ifilot/p2000t-teletekst-cartridge/emulator/src/p2wp_device.c

#include "p2wp_device.h"
#include "../../firmware/src/firmware_core.h"
#include "../../firmware/src/custom_endpoint.h"
#include "../../firmware/src/version.h"

#include <stdbool.h>
#include <stdio.h>
#include <string.h>

enum {
    TX_PORT = 0x40,
    RX_PORT = 0x41,
    STATUS_PORT = 0x42,
    SCREEN_SIZE = 960,
    CHUNK_SIZE = 240,
    FETCH_TIMEOUT_TICKS = 3000,
};

static p2wp_parser_t parser;
static p2wp_firmware_core_t firmware_core;
static p2wp_fetch_fn fetch_page;
static void *fetch_context;
static uint8_t encoded[P2WP_MAX_ENCODED];
static size_t encoded_length;
static size_t encoded_position;
static uint8_t screen[SCREEN_SIZE];
static uint8_t next_subpage;
static uint8_t local_clock[7];
static uint16_t previous_page, next_page;
static uint8_t fetch_state;
static uint8_t fetch_error;
static uint8_t profile_state;
static uint8_t wifi_security;
static uint8_t protocol_maximum = P2WP_MAX_VERSION;
static uint8_t status_length_override;
static int fetch_stall_after = -1;
static unsigned fetch_start_count;
static unsigned fetch_stall_ticks;
static bool fetch_timeout_enabled = true;
static bool clock_valid = true;
static const char *flash_path;
static char stored_custom_url[CUSTOM_ENDPOINT_URL_MAX + 1u];
static uint8_t stored_custom_url_length;
static uint8_t stored_auto_start_source = P2WP_TELETEKST_AUTOSTART_DISABLED;

static const uint8_t flash_magic[8] = {
    'P', '2', 'W', 'P', 'U', 'R', 'L', '1',
};

static uint8_t emulator_capabilities(void *context) {
    (void)context;
    return protocol_maximum >= 3u
        ? P2WP_CAPABILITY_ECHO | P2WP_CAPABILITY_WIFI |
            P2WP_CAPABILITY_INTERNET | P2WP_CAPABILITY_WIFI_PROFILE |
            P2WP_CAPABILITY_DEVICE_INFO | P2WP_CAPABILITY_VERSION_CHECK
        : P2WP_CAPABILITY_ECHO | P2WP_CAPABILITY_WIFI |
            P2WP_CAPABILITY_INTERNET | P2WP_CAPABILITY_WIFI_PROFILE;
}

static uint8_t version_check_start(
    void *context,
    const p2wp_frame_t *request,
    p2wp_frame_t *response
) {
    (void)context;
    (void)request;
    response->payload_length = 0u;
    return P2WP_FIRMWARE_COMMAND_OK;
}

static uint8_t version_check_status(
    void *context,
    const p2wp_frame_t *request,
    p2wp_frame_t *response
) {
    (void)context;
    (void)request;
    response->payload[0] = P2WP_VERSION_CHECK_COMPLETE;
    response->payload[1] = 0u;
    response->payload[2] = P2WP_FIRMWARE_VERSION_MAJOR;
    response->payload[3] = P2WP_FIRMWARE_VERSION_MINOR;
    response->payload[4] = P2WP_FIRMWARE_VERSION_PATCH;
    response->payload_length = 5u;
    return P2WP_FIRMWARE_COMMAND_OK;
}

static uint8_t wifi_scan_start(
    void *context,
    const p2wp_frame_t *request,
    p2wp_frame_t *response
) {
    (void)context;
    (void)request;
    response->payload_length = 0u;
    return P2WP_FIRMWARE_COMMAND_OK;
}

static uint8_t wifi_scan_status(
    void *context,
    const p2wp_frame_t *request,
    p2wp_frame_t *response
) {
    (void)context;
    (void)request;
    response->payload[0] = 2u;
    response->payload[1] = 1u;
    response->payload[2] = 1u;
    response->payload_length = 3u;
    return P2WP_FIRMWARE_COMMAND_OK;
}

static uint8_t wifi_scan_result(
    void *context,
    const p2wp_frame_t *request,
    p2wp_frame_t *response
) {
    (void)context;
    static const char ssid[] = "Emulated WiFi";
    response->payload[0] = request->payload[0];
    response->payload[1] = (uint8_t)-35;
    response->payload[2] = wifi_security;
    response->payload[3] = sizeof(ssid) - 1u;
    memcpy(response->payload + 4u, ssid, sizeof(ssid) - 1u);
    response->payload_length = 4u + sizeof(ssid) - 1u;
    return P2WP_FIRMWARE_COMMAND_OK;
}

static uint8_t wifi_connect(
    void *context,
    const p2wp_frame_t *request,
    p2wp_frame_t *response
) {
    (void)context;
    if ((wifi_security == 0u && request->payload[1] != 0u) ||
        (wifi_security == 1u && request->payload[1] < 8u)) {
        return P2WP_ERROR_INVALID_PAYLOAD;
    }
    response->payload_length = 0u;
    return P2WP_FIRMWARE_COMMAND_OK;
}

static uint8_t wifi_status(
    void *context,
    const p2wp_frame_t *request,
    p2wp_frame_t *response
) {
    (void)context;
    (void)request;
    response->payload[0] = 2u;
    response->payload_length = 1u;
    return P2WP_FIRMWARE_COMMAND_OK;
}

static uint8_t wifi_profile_status(
    void *context,
    const p2wp_frame_t *request,
    p2wp_frame_t *response
) {
    (void)context;
    (void)request;
    response->payload[0] = profile_state;
    response->payload[1] = 0u;
    response->payload_length = 2u;
    return P2WP_FIRMWARE_COMMAND_OK;
}

static uint8_t wifi_profile_connect(
    void *context,
    const p2wp_frame_t *request,
    p2wp_frame_t *response
) {
    (void)context;
    (void)request;
    response->payload_length = 0u;
    return profile_state != 0u
        ? P2WP_FIRMWARE_COMMAND_OK
        : P2WP_ERROR_WIFI_BUSY;
}

static uint8_t wifi_profile_save(
    void *context,
    const p2wp_frame_t *request,
    p2wp_frame_t *response
) {
    (void)context;
    (void)request;
    profile_state = 1u;
    response->payload_length = 0u;
    return P2WP_FIRMWARE_COMMAND_OK;
}

static uint8_t wifi_profile_delete(
    void *context,
    const p2wp_frame_t *request,
    p2wp_frame_t *response
) {
    (void)context;
    (void)request;
    profile_state = 0u;
    response->payload_length = 0u;
    return P2WP_FIRMWARE_COMMAND_OK;
}

static uint8_t teletekst_fetch_start(
    void *context,
    const p2wp_frame_t *request,
    p2wp_frame_t *response
) {
    (void)context;
    const uint16_t page =
        (uint16_t)request->payload[0] |
        ((uint16_t)request->payload[1] << 8u);
    char custom_url[97] = {0};
    if (request->payload[3] == P2WP_TELETEKST_SOURCE_CUSTOM) {
        memcpy(custom_url, request->payload + 5u, request->payload[4]);
    }
    if (request->payload[3] == P2WP_TELETEKST_SOURCE_INTERNATIONAL) {
        if (request->payload[4] == PETSCII_CATALOGUE) {
            fetch_error = petscii_catalogue(request->payload[2], screen)
                ? 0u : P2WP_TELETEKST_ERROR_INVALID_DATA;
            next_subpage = 0u;
            previous_page = next_page = 0u;
            fetch_state = fetch_error ? 4u : 3u;
            response->payload_length = 0u;
            return P2WP_FIRMWARE_COMMAND_OK;
        }
        if (!petscii_channel_url(request->payload[4], custom_url, sizeof(custom_url)))
            return P2WP_ERROR_INVALID_PAYLOAD;
    }
    previous_page = 0u;
    next_page = 0u;
    if (fetch_stall_after >= 0 &&
        fetch_start_count >= (unsigned)fetch_stall_after) {
        fetch_error = 0u;
        fetch_state = 1u;
        fetch_stall_ticks = 0u;
        response->payload_length = 0u;
        return P2WP_FIRMWARE_COMMAND_OK;
    }
    fetch_start_count++;
    fetch_error = fetch_page != NULL ? fetch_page(
        fetch_context,
        request->payload[3],
        custom_url[0] != '\0' ? custom_url : NULL,
        page,
        request->payload[2],
        screen,
        &next_subpage,
        &previous_page,
        &next_page,
        local_clock
    ) : P2WP_TELETEKST_ERROR_INVALID_DATA;
    fetch_state = fetch_error != 0u ? 4u : 3u;
    response->payload_length = 0u;
    return P2WP_FIRMWARE_COMMAND_OK;
}

static uint8_t teletekst_fetch_status(
    void *context,
    const p2wp_frame_t *request,
    p2wp_frame_t *response
) {
    (void)context;
    response->payload[0] = fetch_state;
    response->payload[1] = request->version < 7u &&
        fetch_error >= P2WP_TELETEKST_ERROR_DNS
            ? P2WP_TELETEKST_ERROR_NETWORK
            : fetch_error;
    response->payload[4] = next_subpage;
    if (request->version >= 3u || status_length_override >= 9u) {
        memcpy(response->payload + 5u, local_clock, 3u);
        response->payload[8] = fetch_error != 0u || !clock_valid ? 0u : 1u;
        memcpy(response->payload + 9u, local_clock + 3u, 4u);
        if (request->version >= 4u) {
            response->payload[13] = (uint8_t)previous_page;
            response->payload[14] = (uint8_t)(previous_page >> 8u);
            response->payload[15] = (uint8_t)next_page;
            response->payload[16] = (uint8_t)(next_page >> 8u);
            if (request->version >= 7u) {
                response->payload[17] = 0u;
                response->payload[18] = 0u;
                response->payload[19] = 0u;
                response->payload[20] = 0u;
            }
        }
        response->payload_length = status_length_override != 0u
            ? status_length_override
            : (request->version >= 7u
                ? 21u
                : (request->version >= 4u ? 17u : 13u));
    } else {
        response->payload_length = status_length_override != 0u
            ? status_length_override
            : 5u;
    }
    return P2WP_FIRMWARE_COMMAND_OK;
}

static uint8_t teletekst_fetch_rows(
    void *context,
    const p2wp_frame_t *request,
    p2wp_frame_t *response
) {
    (void)context;
    memcpy(
        response->payload,
        screen + (size_t)request->payload[0] * CHUNK_SIZE,
        CHUNK_SIZE
    );
    response->payload_length = CHUNK_SIZE;
    return P2WP_FIRMWARE_COMMAND_OK;
}

static uint8_t teletekst_custom_url_load(
    void *context,
    const p2wp_frame_t *request,
    p2wp_frame_t *response
) {
    (void)context;
    (void)request;
    response->payload[0] = stored_custom_url_length;
    memcpy(
        response->payload + 1u,
        stored_custom_url,
        stored_custom_url_length
    );
    response->payload_length = (uint16_t)(1u + stored_custom_url_length);
    return P2WP_FIRMWARE_COMMAND_OK;
}

static bool write_flash_settings(void) {
    if (flash_path == NULL) {
        return true;
    }
    FILE *file = fopen(flash_path, "wb");
    if (file == NULL) {
        return false;
    }
    const uint8_t format_marker = 0xfeu;
    const bool wrote = fwrite(flash_magic, 1u, sizeof(flash_magic), file) ==
            sizeof(flash_magic) &&
        fwrite(&format_marker, 1u, 1u, file) == 1u &&
        fwrite(&stored_auto_start_source, 1u, 1u, file) == 1u &&
        fwrite(&stored_custom_url_length, 1u, 1u, file) == 1u &&
        fwrite(stored_custom_url, 1u, stored_custom_url_length, file) ==
            stored_custom_url_length;
    return fclose(file) == 0 && wrote;
}

static uint8_t teletekst_custom_url_save(
    void *context,
    const p2wp_frame_t *request,
    p2wp_frame_t *response
) {
    (void)context;
    const uint8_t url_length = request->payload[0];
    custom_endpoint_t endpoint;
    if (!custom_endpoint_parse(
            (const char *)request->payload + 1u,
            url_length,
            &endpoint
        )) {
        return P2WP_ERROR_INVALID_PAYLOAD;
    }
    if (stored_custom_url_length == url_length &&
        memcmp(stored_custom_url, request->payload + 1u, url_length) == 0) {
        response->payload_length = 0u;
        return P2WP_FIRMWARE_COMMAND_OK;
    }
    char previous_url[CUSTOM_ENDPOINT_URL_MAX + 1u];
    const uint8_t previous_length = stored_custom_url_length;
    memcpy(previous_url, stored_custom_url, sizeof(previous_url));
    memcpy(stored_custom_url, request->payload + 1u, url_length);
    stored_custom_url[url_length] = '\0';
    stored_custom_url_length = url_length;
    if (!write_flash_settings()) {
        memcpy(stored_custom_url, previous_url, sizeof(previous_url));
        stored_custom_url_length = previous_length;
        return P2WP_ERROR_INTERNAL;
    }
    response->payload_length = 0u;
    return P2WP_FIRMWARE_COMMAND_OK;
}

static uint8_t teletekst_settings_load(
    void *context,
    const p2wp_frame_t *request,
    p2wp_frame_t *response
) {
    (void)context;
    (void)request;
    response->payload[0] = stored_auto_start_source;
    response->payload_length = 1u;
    return P2WP_FIRMWARE_COMMAND_OK;
}

static uint8_t teletekst_settings_save(
    void *context,
    const p2wp_frame_t *request,
    p2wp_frame_t *response
) {
    (void)context;
    const uint8_t previous = stored_auto_start_source;
    stored_auto_start_source = request->payload[0];
    if (!write_flash_settings()) {
        stored_auto_start_source = previous;
        return P2WP_ERROR_INTERNAL;
    }
    response->payload_length = 0u;
    return P2WP_FIRMWARE_COMMAND_OK;
}

static const p2wp_firmware_operations_t emulator_operations = {
    .capabilities = emulator_capabilities,
    .version_check_start = version_check_start,
    .version_check_status = version_check_status,
    .wifi_scan_start = wifi_scan_start,
    .wifi_scan_status = wifi_scan_status,
    .wifi_scan_result = wifi_scan_result,
    .wifi_connect = wifi_connect,
    .wifi_status = wifi_status,
    .wifi_profile_status = wifi_profile_status,
    .wifi_profile_connect = wifi_profile_connect,
    .wifi_profile_save = wifi_profile_save,
    .wifi_profile_delete = wifi_profile_delete,
    .teletekst_fetch_start = teletekst_fetch_start,
    .teletekst_fetch_status = teletekst_fetch_status,
    .teletekst_fetch_rows = teletekst_fetch_rows,
    .teletekst_custom_url_load = teletekst_custom_url_load,
    .teletekst_custom_url_save = teletekst_custom_url_save,
    .teletekst_settings_load = teletekst_settings_load,
    .teletekst_settings_save = teletekst_settings_save,
};

void p2wp_device_init(p2wp_fetch_fn fetch, void *context) {
    fetch_page = fetch;
    fetch_context = context;
    p2wp_firmware_core_init(
        &firmware_core,
        &emulator_operations,
        NULL,
        P2WP_HARDWARE_PICO_2_W
    );
    p2wp_device_reset();
}

void p2wp_device_set_protocol_range(uint8_t minimum, uint8_t maximum) {
    protocol_maximum = maximum;
    p2wp_firmware_core_set_protocol_range(
        &firmware_core,
        minimum,
        maximum
    );
    p2wp_device_reset();
}

void p2wp_device_set_status_length(uint8_t length) {
    status_length_override = length;
}

void p2wp_device_set_fetch_stall_after(int successful_fetches) {
    fetch_stall_after = successful_fetches;
    fetch_start_count = 0u;
    fetch_stall_ticks = 0u;
}

void p2wp_device_set_fetch_timeout_enabled(int enabled) {
    fetch_timeout_enabled = enabled != 0;
}

void p2wp_device_set_clock_valid(int valid) {
    clock_valid = valid != 0;
}

void p2wp_device_set_profile_present(int present) {
    profile_state = present ? 1u : 0u;
}

void p2wp_device_set_wifi_security(uint8_t security) {
    wifi_security = security;
}

void p2wp_device_set_flash_path(const char *path) {
    flash_path = path;
    stored_custom_url_length = 0u;
    stored_custom_url[0] = '\0';
    stored_auto_start_source = P2WP_TELETEKST_AUTOSTART_DISABLED;
    if (path == NULL) {
        return;
    }
    FILE *file = fopen(path, "rb");
    if (file == NULL) {
        return;
    }
    uint8_t magic[sizeof(flash_magic)];
    uint8_t first_byte = 0u;
    const bool header_ok =
        fread(magic, 1u, sizeof(magic), file) == sizeof(magic) &&
        memcmp(magic, flash_magic, sizeof(magic)) == 0 &&
        fread(&first_byte, 1u, 1u, file) == 1u;
    uint8_t url_length = first_byte;
    uint8_t auto_start_source = P2WP_TELETEKST_AUTOSTART_DISABLED;
    const bool current_format = header_ok && first_byte == 0xfeu;
    bool settings_ok = header_ok;
    if (current_format) {
        settings_ok = fread(&auto_start_source, 1u, 1u, file) == 1u &&
            (auto_start_source == P2WP_TELETEKST_AUTOSTART_DISABLED ||
             auto_start_source <= P2WP_TELETEKST_MENU_SOURCE_ARCHIVE) &&
            fread(&url_length, 1u, 1u, file) == 1u;
    }
    if (settings_ok && current_format && url_length == 0u && fgetc(file) == EOF) {
        stored_auto_start_source = auto_start_source;
        fclose(file);
        return;
    }
    const bool url_ok = settings_ok &&
        url_length > 0u && url_length <= CUSTOM_ENDPOINT_URL_MAX &&
        fread(stored_custom_url, 1u, url_length, file) == url_length &&
        fgetc(file) == EOF;
    fclose(file);
    custom_endpoint_t endpoint;
    if (!url_ok || !custom_endpoint_parse(
            stored_custom_url,
            url_length,
            &endpoint
        )) {
        stored_custom_url[0] = '\0';
        stored_custom_url_length = 0u;
        return;
    }
    stored_custom_url[url_length] = '\0';
    stored_custom_url_length = url_length;
    stored_auto_start_source = auto_start_source;
}

void p2wp_device_reset(void) {
    p2wp_parser_init(&parser);
    p2wp_firmware_core_reset(&firmware_core);
    encoded_length = 0u;
    encoded_position = 0u;
    fetch_state = 0u;
    fetch_error = 0u;
    fetch_stall_ticks = 0u;
    next_subpage = 0u;
    previous_page = 0u;
    next_page = 0u;
    profile_state = 0u;
    wifi_security = 0u;
    memset(screen, 0, sizeof(screen));
}

void p2wp_device_tick(void) {
    if (fetch_timeout_enabled && fetch_state == 1u &&
        ++fetch_stall_ticks >= FETCH_TIMEOUT_TICKS) {
        fetch_state = 4u;
        fetch_error = P2WP_TELETEKST_ERROR_TIMEOUT;
    }
}

void p2wp_device_out(uint8_t port, uint8_t value) {
    if (port != TX_PORT) {
        return;
    }
    p2wp_frame_t request;
    const p2wp_parse_result_t result = p2wp_parser_feed(
        &parser,
        value,
        &request
    );
    if (result != P2WP_PARSE_FRAME) {
        return;
    }
    p2wp_frame_t response;
    p2wp_firmware_core_handle(&firmware_core, &request, &response);
    encoded_length = p2wp_encode(&response, encoded, sizeof(encoded));
    encoded_position = 0u;
}

uint8_t p2wp_device_in(uint8_t port) {
    if (port == STATUS_PORT) {
        return 2u | (encoded_position < encoded_length ? 1u : 0u);
    }
    if (port == RX_PORT && encoded_position < encoded_length) {
        return encoded[encoded_position++];
    }
    return 0xffu;
}
