ifilot/p2000t-teletekst-cartridge/src/version.h

/**
 * @file version.h
 * @brief Cartridge release version shared by the UI and release checks.
 *
 * SPDX-License-Identifier: GPL-3.0-only
 * This file is part of the P2000T Teletekst cartridge and is licensed under
 * version 3 of the GNU General Public License. See the repository LICENSE.
 */

#ifndef P2000T_VERSION_H_
#define P2000T_VERSION_H_

/** Cartridge release major version. */
#define P2WP_CARTRIDGE_VERSION_MAJOR 0u
/** Cartridge release minor version. */
#define P2WP_CARTRIDGE_VERSION_MINOR 5u
/** Cartridge release patch version. */
#define P2WP_CARTRIDGE_VERSION_PATCH 0u
/** Cartridge release version formatted for display. */
#define P2WP_CARTRIDGE_VERSION "0.5.0"

#endif  // P2000T_VERSION_H_
