ifilot/p2000t-teletekst-cartridge/firmware/src/mbedtls_config.h

#ifndef P2WP_MBEDTLS_CONFIG_H
#define P2WP_MBEDTLS_CONFIG_H

// Minimal Pico W TLS 1.2 client configuration, based on Raspberry Pi's
// pico-examples Wi-Fi configuration. Certificate dates are not checked because
// the Pico has no trusted wall clock at startup; the CA chain and hostname are.
#include <limits.h>

#define MBEDTLS_NO_PLATFORM_ENTROPY
#define MBEDTLS_ENTROPY_HARDWARE_ALT
#define MBEDTLS_SSL_OUT_CONTENT_LEN 2048
#define MBEDTLS_ALLOW_PRIVATE_ACCESS
#define MBEDTLS_HAVE_TIME
#define MBEDTLS_PLATFORM_MS_TIME_ALT

#define MBEDTLS_CIPHER_MODE_CBC
#define MBEDTLS_ECP_DP_SECP256R1_ENABLED
#define MBEDTLS_ECP_DP_SECP384R1_ENABLED
#define MBEDTLS_ECP_DP_CURVE25519_ENABLED
#define MBEDTLS_KEY_EXCHANGE_RSA_ENABLED
#define MBEDTLS_KEY_EXCHANGE_ECDHE_RSA_ENABLED
#define MBEDTLS_KEY_EXCHANGE_ECDHE_ECDSA_ENABLED
#define MBEDTLS_PKCS1_V15
#define MBEDTLS_SHA256_SMALLER
#define MBEDTLS_SSL_SERVER_NAME_INDICATION
#define MBEDTLS_AES_C
#define MBEDTLS_ASN1_PARSE_C
#define MBEDTLS_ASN1_WRITE_C
#define MBEDTLS_BASE64_C
#define MBEDTLS_BIGNUM_C
#define MBEDTLS_CIPHER_C
#define MBEDTLS_CTR_DRBG_C
#define MBEDTLS_ECDH_C
#define MBEDTLS_ECDSA_C
#define MBEDTLS_ECP_C
#define MBEDTLS_ENTROPY_C
#define MBEDTLS_ERROR_C
#define MBEDTLS_GCM_C
#define MBEDTLS_MD_C
#define MBEDTLS_OID_C
#define MBEDTLS_PEM_PARSE_C
#define MBEDTLS_PK_C
#define MBEDTLS_PK_PARSE_C
#define MBEDTLS_PLATFORM_C
#define MBEDTLS_RSA_C
#define MBEDTLS_SHA1_C
#define MBEDTLS_SHA224_C
#define MBEDTLS_SHA256_C
#define MBEDTLS_SHA384_C
#define MBEDTLS_SHA512_C
#define MBEDTLS_SSL_CLI_C
#define MBEDTLS_SSL_PROTO_TLS1_2
#define MBEDTLS_SSL_TLS_C
#define MBEDTLS_X509_CRT_PARSE_C
#define MBEDTLS_X509_USE_C
#define MBEDTLS_AES_FEWER_TABLES
#define MBEDTLS_ECP_NIST_OPTIM

#endif
