ifilot/p2000t-teletekst-cartridge/src/ui.c

/**
 * @file ui.c
 * @brief Reusable SAA5050 panels, opening artwork, and footer components.
 *
 * SPDX-License-Identifier: GPL-3.0-only
 * This file is part of the P2000T Teletekst cartridge and is licensed under
 * version 3 of the GNU General Public License. See the repository LICENSE.
 */

#include "ui.h"

#include "build_info.h"
#include "lz4_z80.h"
#include "platform.h"
#include "ui_screens.h"
#include "version.h"

enum {
  SAA_ALPHA_BLUE = 0x04,
  SAA_ALPHA_WHITE = 0x07,
  SAA_GRAPHICS_BLUE = 0x14,
  SAA_GRAPHICS_WHITE = 0x17,
  SAA_NEW_BACKGROUND = 0x1d,
};

/** Raw LZ4 block for the complete 24x40 SAA5050 opening screen. */
static const uint8_t opening_screen_lz4[] = {
    0x4fu, 0x04u, 0x1du, 0x07u, 0x20u, 0x01u, 0x00u, 0x11u, 0x0fu, 0x28u, 0x00u,
    0x1cu, 0xf5u, 0x0bu, 0x50u, 0x32u, 0x30u, 0x30u, 0x30u, 0x54u, 0x20u, 0x20u,
    0x49u, 0x4eu, 0x54u, 0x45u, 0x52u, 0x4eu, 0x45u, 0x54u, 0x20u, 0x54u, 0x45u,
    0x4cu, 0x45u, 0x54u, 0x45u, 0x4bu, 0x53u, 0x54u, 0x28u, 0x00u, 0x12u, 0x17u,
    0x09u, 0x00u, 0x1fu, 0x70u, 0x01u, 0x00u, 0x04u, 0x0cu, 0x28u, 0x00u, 0x4fu,
    0x35u, 0x20u, 0x20u, 0x6au, 0x04u, 0x00u, 0x01u, 0x0du, 0x28u, 0x00u, 0x78u,
    0x6au, 0x35u, 0x6au, 0x7fu, 0x7fu, 0x35u, 0x6au, 0x02u, 0x00u, 0x4fu, 0x7fu,
    0x35u, 0x6au, 0x23u, 0x50u, 0x00u, 0x06u, 0x0au, 0x28u, 0x00u, 0x1eu, 0x20u,
    0x50u, 0x00u, 0x2cu, 0x7fu, 0x7fu, 0x52u, 0x00u, 0x0fu, 0x28u, 0x00u, 0x06u,
    0x0bu, 0x9cu, 0x00u, 0x0au, 0x28u, 0x00u, 0x20u, 0x3cu, 0x2cu, 0x01u, 0x00u,
    0x1fu, 0x2fu, 0x01u, 0x00u, 0x03u, 0x11u, 0x2cu, 0x01u, 0x00u, 0x10u, 0x34u,
    0x28u, 0x00u, 0x1fu, 0x35u, 0x66u, 0x01u, 0x0fu, 0x10u, 0x35u, 0x28u, 0x00u,
    0x66u, 0x75u, 0x70u, 0x70u, 0x30u, 0x20u, 0x60u, 0x32u, 0x01u, 0x09u, 0x0du,
    0x00u, 0x11u, 0x70u, 0x5au, 0x01u, 0x00u, 0x28u, 0x00u, 0xe1u, 0x20u, 0x20u,
    0x20u, 0x17u, 0x35u, 0x20u, 0x6au, 0x20u, 0x60u, 0x70u, 0x35u, 0x20u, 0x7fu,
    0x7fu, 0x07u, 0x00u, 0x02u, 0x0du, 0x00u, 0x00u, 0x02u, 0x00u, 0x21u, 0x70u,
    0x7au, 0x0au, 0x01u, 0x17u, 0x20u, 0x28u, 0x00u, 0x21u, 0x2au, 0x2fu, 0x28u,
    0x00u, 0x24u, 0x2au, 0x2fu, 0x0du, 0x00u, 0x6du, 0x65u, 0x70u, 0x35u, 0x20u,
    0x2fu, 0x6fu, 0x28u, 0x00u, 0x21u, 0x68u, 0x7cu, 0x28u, 0x00u, 0x24u, 0x68u,
    0x7cu, 0x0du, 0x00u, 0x6du, 0x34u, 0x20u, 0x7du, 0x7cu, 0x20u, 0x6au, 0x28u,
    0x00u, 0x61u, 0x22u, 0x23u, 0x35u, 0x20u, 0x23u, 0x6bu, 0x07u, 0x00u, 0x02u,
    0x0du, 0x00u, 0x45u, 0x35u, 0x20u, 0x37u, 0x23u, 0x28u, 0x00u, 0x7fu, 0x17u,
    0x7cu, 0x7cu, 0x7cu, 0x7cu, 0x70u, 0x73u, 0x01u, 0x00u, 0x09u, 0x81u, 0x71u,
    0x78u, 0x7cu, 0x7cu, 0x7cu, 0x07u, 0x1du, 0x04u, 0xfau, 0x00u, 0xf5u, 0x08u,
    0x55u, 0x57u, 0x20u, 0x56u, 0x45u, 0x4eu, 0x53u, 0x54u, 0x45u, 0x52u, 0x20u,
    0x4fu, 0x50u, 0x20u, 0x44u, 0x45u, 0x20u, 0x57u, 0x45u, 0x52u, 0x45u, 0x4cu,
    0x44u, 0x1au, 0x01u, 0x04u, 0x28u, 0x00u, 0x64u, 0x4eu, 0x4fu, 0x53u, 0x20u,
    0x45u, 0x4eu, 0x88u, 0x02u, 0x0cu, 0x7eu, 0x02u, 0x03u, 0xa8u, 0x02u, 0xf4u,
    0x0cu, 0x4fu, 0x52u, 0x49u, 0x47u, 0x49u, 0x4eu, 0x45u, 0x45u, 0x4cu, 0x20u,
    0x53u, 0x41u, 0x41u, 0x35u, 0x30u, 0x35u, 0x30u, 0x2du, 0x4du, 0x4fu, 0x5au,
    0x41u, 0x49u, 0x45u, 0x4bu, 0x42u, 0x45u, 0x54u, 0x00u, 0x01u, 0x28u, 0x00u,
    0x91u, 0x4bu, 0x4cu, 0x41u, 0x53u, 0x53u, 0x49u, 0x45u, 0x4bu, 0x20u, 0x18u,
    0x00u, 0x60u, 0x2cu, 0x20u, 0x41u, 0x43u, 0x54u, 0x55u, 0x36u, 0x00u, 0x61u,
    0x4eu, 0x49u, 0x45u, 0x55u, 0x57u, 0x53u, 0x28u, 0x00u, 0x2fu, 0x14u, 0x20u,
    0x01u, 0x00u, 0x5eu, 0x50u, 0x20u, 0x20u, 0x20u, 0x20u, 0x20u};
/** RAM workspace receiving the decompressed opening screen. */
static uint8_t opening_screen[24u * P2000T_SCREEN_COLUMNS];

/**
 * @brief Expands the opening screen and resets graphics mode on its first row.
 *
 * Real SAA5050 hardware can otherwise retain alpha mode at the start of the
 * mosaic. Repeating the colour/background/graphics controls prevents the
 * first graphics byte from appearing as `P` and restores the top stroke.
 */
static void prepare_opening_screen(void) {
  lz4_decompress(opening_screen_lz4, opening_screen,
                 sizeof(opening_screen_lz4));
  opening_screen[3u * P2000T_SCREEN_COLUMNS + 3u] = SAA_ALPHA_BLUE;
  opening_screen[3u * P2000T_SCREEN_COLUMNS + 4u] = SAA_NEW_BACKGROUND;
  opening_screen[3u * P2000T_SCREEN_COLUMNS + 5u] = SAA_GRAPHICS_WHITE;
}

/* Uncompressed reference retained next to the generated block for review. */
#if 0
/* Joined P2000T/TELETEKST mosaic. Each entry is one complete, display-ready
 * 40-column SAA5050 row. */
static const uint8_t opening_logo[14][40] = {
    {0x04, 0x1d, 0x17, 0x04, 0x1d, 0x17, 0x20, 0x20, 0x20, 0x70,
     0x70, 0x70, 0x70, 0x70, 0x70, 0x70, 0x70, 0x70, 0x70, 0x70,
     0x70, 0x70, 0x70, 0x70, 0x70, 0x70, 0x70, 0x70, 0x70, 0x70,
     0x70, 0x70, 0x70, 0x20, 0x20, 0x20, 0x20, 0x20, 0x20, 0x20},
    {0x04, 0x1d, 0x17, 0x20, 0x20, 0x20, 0x20, 0x20, 0x20, 0x35,
     0x20, 0x20, 0x6a, 0x35, 0x20, 0x20, 0x6a, 0x35, 0x20, 0x20,
     0x6a, 0x35, 0x20, 0x20, 0x6a, 0x35, 0x20, 0x20, 0x6a, 0x35,
     0x20, 0x20, 0x6a, 0x20, 0x20, 0x20, 0x20, 0x20, 0x20, 0x20},
    {0x04, 0x1d, 0x17, 0x20, 0x20, 0x20, 0x20, 0x20, 0x20, 0x35,
     0x6a, 0x35, 0x6a, 0x7f, 0x7f, 0x35, 0x6a, 0x35, 0x6a, 0x35,
     0x6a, 0x35, 0x6a, 0x35, 0x6a, 0x35, 0x6a, 0x35, 0x6a, 0x7f,
     0x35, 0x6a, 0x23, 0x20, 0x20, 0x20, 0x20, 0x20, 0x20, 0x20},
    {0x04, 0x1d, 0x17, 0x20, 0x20, 0x20, 0x20, 0x20, 0x20, 0x35,
     0x20, 0x20, 0x6a, 0x35, 0x20, 0x20, 0x6a, 0x35, 0x6a, 0x35,
     0x6a, 0x35, 0x6a, 0x35, 0x6a, 0x35, 0x6a, 0x35, 0x6a, 0x7f,
     0x35, 0x6a, 0x20, 0x20, 0x20, 0x20, 0x20, 0x20, 0x20, 0x20},
    {0x04, 0x1d, 0x17, 0x20, 0x20, 0x20, 0x20, 0x20, 0x20, 0x35,
     0x6a, 0x7f, 0x7f, 0x35, 0x6a, 0x7f, 0x7f, 0x35, 0x6a, 0x35,
     0x6a, 0x35, 0x6a, 0x35, 0x6a, 0x35, 0x6a, 0x35, 0x6a, 0x7f,
     0x35, 0x6a, 0x20, 0x20, 0x20, 0x20, 0x20, 0x20, 0x20, 0x20},
    {0x04, 0x1d, 0x17, 0x20, 0x20, 0x20, 0x20, 0x20, 0x20, 0x35,
     0x6a, 0x7f, 0x7f, 0x35, 0x20, 0x20, 0x6a, 0x35, 0x20, 0x20,
     0x6a, 0x35, 0x20, 0x20, 0x6a, 0x35, 0x20, 0x20, 0x6a, 0x7f,
     0x35, 0x6a, 0x20, 0x20, 0x20, 0x20, 0x20, 0x20, 0x20, 0x20},
    {0x04, 0x1d, 0x17, 0x3c, 0x2c, 0x2c, 0x2c, 0x2c, 0x2c, 0x2f,
     0x2f, 0x2f, 0x2f, 0x2f, 0x2f, 0x2f, 0x2f, 0x2f, 0x2f, 0x2f,
     0x2f, 0x2f, 0x2f, 0x2f, 0x2f, 0x2f, 0x2f, 0x2f, 0x2f, 0x2f,
     0x2f, 0x2f, 0x2c, 0x2c, 0x2c, 0x2c, 0x2c, 0x2c, 0x34, 0x20},
    {0x04, 0x1d, 0x17, 0x35, 0x20, 0x20, 0x20, 0x20, 0x20, 0x20,
     0x20, 0x20, 0x20, 0x20, 0x20, 0x20, 0x20, 0x20, 0x20, 0x20,
     0x20, 0x20, 0x20, 0x20, 0x20, 0x20, 0x20, 0x20, 0x20, 0x20,
     0x20, 0x20, 0x20, 0x20, 0x20, 0x20, 0x20, 0x20, 0x35, 0x20},
    {0x04, 0x1d, 0x17, 0x75, 0x70, 0x70, 0x30, 0x20, 0x60, 0x70,
     0x70, 0x70, 0x70, 0x70, 0x70, 0x70, 0x70, 0x70, 0x70, 0x30,
     0x20, 0x60, 0x70, 0x70, 0x70, 0x70, 0x70, 0x70, 0x70, 0x70,
     0x70, 0x70, 0x70, 0x20, 0x20, 0x70, 0x70, 0x70, 0x35, 0x20},
    {0x04, 0x1d, 0x20, 0x20, 0x20, 0x17, 0x35, 0x20, 0x6a, 0x20,
     0x60, 0x70, 0x35, 0x20, 0x7f, 0x7f, 0x20, 0x60, 0x70, 0x35,
     0x20, 0x6a, 0x20, 0x60, 0x70, 0x35, 0x20, 0x35, 0x20, 0x35,
     0x20, 0x70, 0x7a, 0x20, 0x20, 0x35, 0x20, 0x20, 0x20, 0x20},
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
};
#endif

/**
 * @brief Clears and writes one full-width styled text row.
 * @param[in] row Screen row to update.
 * @param[in] foreground SAA5050 colour control used as the new background.
 * @param[in] text_colour SAA5050 alpha colour used for the text.
 * @param[in] text Null-terminated row text, starting after the control prefix.
 */
static void styled_line(uint8_t row, uint8_t foreground, uint8_t text_colour,
                        const char *text) {
  uint8_t prefix[3];
  platform_clear_line(row);
  prefix[0] = foreground;
  prefix[1] = SAA_NEW_BACKGROUND;
  prefix[2] = text_colour;
  platform_write_bytes(row, 0u, prefix, sizeof(prefix));
  platform_write_text(row, 3u, text);
}

/* Public API contract: see ui.h. */
void ui_title(uint8_t row, const char *text) {
  styled_line(row, SAA_ALPHA_BLUE, SAA_ALPHA_WHITE, text);
}

/* Public API contract: see ui.h. */
void ui_panel(uint8_t row, const char *text) {
  styled_line(row, SAA_ALPHA_WHITE, SAA_ALPHA_BLUE, text);
}

/* Public API contract: see ui.h. */
void ui_rule(uint8_t row) {
  static const uint8_t graphics_blue[] = {SAA_GRAPHICS_BLUE};
  static const uint8_t mosaic_rule[] = {0x73};
  uint8_t column;
  platform_clear_line(row);
  platform_write_bytes(row, 0u, graphics_blue, 1u);
  for (column = 1u; column != P2000T_SCREEN_COLUMNS; ++column)
    platform_write_bytes(row, column, mosaic_rule, 1u);
}

/* Public API contract: see ui.h. */
void ui_footer(void) {
  ui_title(23u, "P2000T Teletekst Cartridge     v" P2WP_CARTRIDGE_VERSION);
}

/* Public API contract: see ui.h. */
void ui_build_info(void) {
  lz4_decompress(build_info_lz4, opening_screen, sizeof(build_info_lz4));
  platform_present_screen(opening_screen);
  platform_write_text(10u, 3u, P2WP_BUILD_TIMESTAMP);
  ui_footer();
}

/* Public API contract: see ui.h. */
void ui_save_prompt(void) {
  lz4_decompress(save_prompt_lz4, opening_screen, sizeof(save_prompt_lz4));
  platform_present_screen(opening_screen);
  ui_footer();
}

/* Public API contract: see ui.h. */
void ui_draw_logo(uint8_t row) {
  uint8_t logo_row;
  prepare_opening_screen();
  for (logo_row = 0u; logo_row != 14u; ++logo_row)
    platform_write_bytes((uint8_t)(row + logo_row), 0u,
                         opening_screen + (uint16_t)(logo_row + 3u) * 40u, 40u);
}

/* Public API contract: see ui.h. */
void ui_opening_screen(void) {
  prepare_opening_screen();
  platform_present_screen(opening_screen);
  platform_write_bytes(22u, 0u, (const uint8_t *)"\007   DRUK OP EEN TOETS",
                       22u);
  ui_footer();
}

/* Public API contract: see ui.h. */
uint8_t ui_wait_opening(void) {
  uint16_t next_second = (uint16_t)(platform_clock() + 50u);
  uint16_t deadline = (uint16_t)(platform_clock() + 3000u);
  uint16_t next_blink = (uint16_t)(platform_clock() + 25u);
  uint8_t seconds = 60u;
  uint8_t visible = 1u;

  platform_write_u8(22u, 33u, seconds);
  for (;;) {
    uint16_t now;
    uint8_t status = platform_key_status();
    if (status != 0u) {
      (void)platform_read_key();
      return 0u;
    }
    now = platform_clock();
    if ((int16_t)(now - deadline) >= 0) {
      platform_write_text(22u, 33u, " 0");
      return 1u;
    }
    if ((int16_t)(now - next_second) >= 0) {
      next_second = (uint16_t)(next_second + 50u);
      --seconds;
      platform_write_text(22u, 33u, "  ");
      platform_write_u8(22u, 33u, seconds);
    }
    if ((int16_t)(now - next_blink) >= 0) {
      next_blink = (uint16_t)(next_blink + 25u);
      visible ^= 1u;
      platform_write_text(22u, 4u,
                          visible ? "DRUK OP EEN TOETS" : "                 ");
    }
  }
}

/* Public API contract: see ui.h. */
void ui_custom_setup(void) {
  lz4_decompress(custom_setup_lz4, opening_screen, sizeof(custom_setup_lz4));
  platform_present_screen(opening_screen);
  ui_footer();
}

/* Public API contract: see ui.h. */
void ui_wifi_scan(void) {
  lz4_decompress(wifi_scan_lz4, opening_screen, sizeof(wifi_scan_lz4));
  platform_present_screen(opening_screen);
}
