ifilot/p2000t-teletekst-cartridge/src/ui_screens.h

/**
 * @file ui_screens.h
 * @brief Compressed auxiliary screens using the shared title/panel palette.
 * SPDX-License-Identifier: GPL-3.0-only
 */

/** Compressed 24x40 build info screen. */
static const uint8_t build_info_lz4[] = {
    0xffu, 0x10u, 0x04u, 0x1du, 0x07u, 0x20u, 0x50u, 0x32u, 0x30u, 0x30u, 0x30u,
    0x54u, 0x20u, 0x54u, 0x45u, 0x4cu, 0x45u, 0x54u, 0x45u, 0x4bu, 0x53u, 0x54u,
    0x20u, 0x20u, 0x49u, 0x4eu, 0x46u, 0x4fu, 0x20u, 0x32u, 0x2fu, 0x32u, 0x20u,
    0x01u, 0x00u, 0x1eu, 0xcfu, 0x03u, 0x20u, 0x43u, 0x4fu, 0x4du, 0x50u, 0x49u,
    0x4cu, 0x41u, 0x54u, 0x49u, 0x45u, 0x28u, 0x00u, 0x09u, 0x13u, 0x06u, 0x28u,
    0x00u, 0x2fu, 0x45u, 0x52u, 0x50u, 0x00u, 0x0bu, 0xffu, 0x0au, 0x07u, 0x20u,
    0x5au, 0x38u, 0x38u, 0x44u, 0x4bu, 0x20u, 0x32u, 0x2eu, 0x34u, 0x20u, 0x2fu,
    0x20u, 0x53u, 0x44u, 0x43u, 0x43u, 0x20u, 0x2du, 0x20u, 0x5au, 0x38u, 0x30u,
    0x20u, 0x01u, 0x00u, 0x74u, 0xcfu, 0x03u, 0x20u, 0x47u, 0x45u, 0x42u, 0x4fu,
    0x55u, 0x57u, 0x44u, 0x20u, 0x4fu, 0x50u, 0x50u, 0x00u, 0x31u, 0x1fu, 0x07u,
    0xc8u, 0x00u, 0x66u, 0xffu, 0x0bu, 0x42u, 0x52u, 0x4fu, 0x4eu, 0x43u, 0x4fu,
    0x44u, 0x45u, 0x20u, 0x45u, 0x4eu, 0x20u, 0x4eu, 0x49u, 0x45u, 0x55u, 0x57u,
    0x45u, 0x20u, 0x56u, 0x45u, 0x52u, 0x53u, 0x49u, 0x45u, 0x53u, 0x50u, 0x00u,
    0x21u, 0xffu, 0x05u, 0x06u, 0x20u, 0x67u, 0x69u, 0x74u, 0x68u, 0x75u, 0x62u,
    0x2eu, 0x63u, 0x6fu, 0x6du, 0x2fu, 0x69u, 0x66u, 0x69u, 0x6cu, 0x6fu, 0x74u,
    0x2fu, 0xf0u, 0x00u, 0x03u, 0x10u, 0x70u, 0x7eu, 0x02u, 0xffu, 0x06u, 0x74u,
    0x2du, 0x74u, 0x65u, 0x6cu, 0x65u, 0x74u, 0x65u, 0x6bu, 0x73u, 0x74u, 0x2du,
    0x63u, 0x61u, 0x72u, 0x74u, 0x72u, 0x69u, 0x64u, 0x67u, 0x65u, 0xe0u, 0x01u,
    0x71u, 0xffu, 0x12u, 0x07u, 0x20u, 0x44u, 0x52u, 0x55u, 0x4bu, 0x20u, 0x45u,
    0x45u, 0x4eu, 0x20u, 0x54u, 0x4fu, 0x45u, 0x54u, 0x53u, 0x20u, 0x4fu, 0x4du,
    0x20u, 0x54u, 0x45u, 0x52u, 0x55u, 0x47u, 0x20u, 0x54u, 0x45u, 0x20u, 0x47u,
    0x41u, 0x41u, 0x4eu, 0x50u, 0x00u, 0x1cu, 0x90u, 0x04u, 0x1du, 0x07u, 0x31u,
    0x3au, 0x20u, 0x48u, 0x55u, 0x4cu, 0x2eu, 0x02u, 0x62u, 0x41u, 0x4eu, 0x44u,
    0x45u, 0x52u, 0x45u, 0x59u, 0x00u, 0x13u, 0x3au, 0x57u, 0x00u, 0x0fu, 0x01u,
    0x00u, 0x17u, 0x50u, 0x20u, 0x20u, 0x20u, 0x20u, 0x20u,
};

/** Compressed 24x40 save prompt screen. */
static const uint8_t save_prompt_lz4[] = {
    0xf8u, 0x0du, 0x04u, 0x1du, 0x07u, 0x20u, 0x50u, 0x32u, 0x30u, 0x30u, 0x30u,
    0x54u, 0x20u, 0x20u, 0x57u, 0x49u, 0x46u, 0x49u, 0x2du, 0x49u, 0x4eu, 0x53u,
    0x54u, 0x45u, 0x4cu, 0x4cu, 0x49u, 0x4eu, 0x47u, 0x20u, 0x01u, 0x00u, 0x00u,
    0x28u, 0x00u, 0x0fu, 0x01u, 0x00u, 0x11u, 0x4fu, 0x04u, 0x1du, 0x16u, 0x73u,
    0x01u, 0x00u, 0x11u, 0x0fu, 0x50u, 0x00u, 0x15u, 0xa0u, 0x07u, 0x1du, 0x04u,
    0x56u, 0x45u, 0x52u, 0x42u, 0x49u, 0x4eu, 0x44u, 0x92u, 0x00u, 0x8eu, 0x47u,
    0x45u, 0x53u, 0x4cu, 0x41u, 0x41u, 0x47u, 0x44u, 0x78u, 0x00u, 0x0fu, 0x50u,
    0x00u, 0x18u, 0x01u, 0xe7u, 0x00u, 0xffu, 0x05u, 0x50u, 0x52u, 0x4fu, 0x46u,
    0x49u, 0x45u, 0x4cu, 0x20u, 0x42u, 0x45u, 0x57u, 0x41u, 0x52u, 0x45u, 0x4eu,
    0x3fu, 0x20u, 0x4au, 0x2fu, 0x4eu, 0xf0u, 0x00u, 0x23u, 0x0fu, 0x28u, 0x00u,
    0x16u, 0x24u, 0x4au, 0x3au, 0x6eu, 0x00u, 0xffu, 0x04u, 0x20u, 0x56u, 0x4fu,
    0x4fu, 0x52u, 0x20u, 0x56u, 0x4fu, 0x4cu, 0x47u, 0x45u, 0x4eu, 0x44u, 0x45u,
    0x20u, 0x4bu, 0x45u, 0x45u, 0x52u, 0x50u, 0x00u, 0x20u, 0xffu, 0x06u, 0x4eu,
    0x3au, 0x20u, 0x41u, 0x4cu, 0x4cu, 0x45u, 0x45u, 0x4eu, 0x20u, 0x44u, 0x45u,
    0x5au, 0x45u, 0x20u, 0x53u, 0x45u, 0x53u, 0x53u, 0x49u, 0x45u, 0xa0u, 0x00u,
    0x28u, 0x0fu, 0xe0u, 0x01u, 0x61u, 0x00u, 0x78u, 0x00u, 0xf0u, 0x01u, 0x4bu,
    0x49u, 0x45u, 0x53u, 0x20u, 0x4au, 0x20u, 0x4fu, 0x46u, 0x20u, 0x4eu, 0x20u,
    0x4fu, 0x4du, 0x20u, 0x44u, 0x1cu, 0x01u, 0x7fu, 0x54u, 0x45u, 0x20u, 0x47u,
    0x41u, 0x41u, 0x4eu, 0x90u, 0x01u, 0x4au, 0x0fu, 0x28u, 0x00u, 0xadu, 0x50u,
    0x20u, 0x20u, 0x20u, 0x20u, 0x20u,
};

/** Compressed custom setup screen; row text retained for review.
 * 1: title  P2000T  EIGEN TELETEKSTSERVER
 * 2: rule
 * 3: panel  BASISADRES VAN UW EIGEN SERVER
 * 4: panel  PICO ONTHOUDT ALLEEN EEN NIEUW ADRES
 * 5: panel  VOORBEELD  http://terra:8080
 * 6: panel  HTTPS: CERTIFICAATCONTROLE STAAT UIT
 * 8: title  SERVERADRES                 MAX. 96
 * 9: panel
 * 10: panel
 * 11: panel
 * 13: panel  ENTER OPSLAAN BS WIS STOP TERUG
 * 22: rule
 */
static const uint8_t custom_setup_lz4[] = {
    0x1fu, 0x20u, 0x01u, 0x00u, 0x14u, 0xf3u, 0x12u, 0x04u, 0x1du, 0x07u, 0x20u,
    0x50u, 0x32u, 0x30u, 0x30u, 0x30u, 0x54u, 0x20u, 0x20u, 0x45u, 0x49u, 0x47u,
    0x45u, 0x4eu, 0x20u, 0x54u, 0x45u, 0x4cu, 0x45u, 0x54u, 0x45u, 0x4bu, 0x53u,
    0x54u, 0x53u, 0x45u, 0x52u, 0x56u, 0x45u, 0x52u, 0x28u, 0x00u, 0x2fu, 0x14u,
    0x73u, 0x01u, 0x00u, 0x13u, 0xf3u, 0x06u, 0x07u, 0x1du, 0x04u, 0x20u, 0x42u,
    0x41u, 0x53u, 0x49u, 0x53u, 0x41u, 0x44u, 0x52u, 0x45u, 0x53u, 0x20u, 0x56u,
    0x41u, 0x4eu, 0x20u, 0x55u, 0x57u, 0x5au, 0x00u, 0x08u, 0x51u, 0x00u, 0x00u,
    0x28u, 0x00u, 0xf0u, 0x06u, 0x50u, 0x49u, 0x43u, 0x4fu, 0x20u, 0x4fu, 0x4eu,
    0x54u, 0x48u, 0x4fu, 0x55u, 0x44u, 0x54u, 0x20u, 0x41u, 0x4cu, 0x4cu, 0x45u,
    0x45u, 0x4eu, 0x20u, 0x04u, 0x00u, 0x61u, 0x4eu, 0x49u, 0x45u, 0x55u, 0x57u,
    0x20u, 0x42u, 0x00u, 0x00u, 0x28u, 0x00u, 0xf6u, 0x0fu, 0x56u, 0x4fu, 0x4fu,
    0x52u, 0x42u, 0x45u, 0x45u, 0x4cu, 0x44u, 0x20u, 0x20u, 0x68u, 0x74u, 0x74u,
    0x70u, 0x3au, 0x2fu, 0x2fu, 0x74u, 0x65u, 0x72u, 0x72u, 0x61u, 0x3au, 0x38u,
    0x30u, 0x38u, 0x30u, 0x20u, 0x20u, 0x50u, 0x00u, 0xffu, 0x15u, 0x48u, 0x54u,
    0x54u, 0x50u, 0x53u, 0x3au, 0x20u, 0x43u, 0x45u, 0x52u, 0x54u, 0x49u, 0x46u,
    0x49u, 0x43u, 0x41u, 0x41u, 0x54u, 0x43u, 0x4fu, 0x4eu, 0x54u, 0x52u, 0x4fu,
    0x4cu, 0x45u, 0x20u, 0x53u, 0x54u, 0x41u, 0x41u, 0x54u, 0x20u, 0x55u, 0x49u,
    0x54u, 0x18u, 0x01u, 0x19u, 0x02u, 0xb0u, 0x00u, 0x02u, 0xc9u, 0x00u, 0x0cu,
    0x01u, 0x00u, 0x71u, 0x4du, 0x41u, 0x58u, 0x2eu, 0x20u, 0x39u, 0x36u, 0x78u,
    0x00u, 0x0fu, 0x01u, 0x00u, 0x11u, 0x0fu, 0x28u, 0x00u, 0x3du, 0x0eu, 0x01u,
    0x00u, 0x0fu, 0x50u, 0x00u, 0x07u, 0xffu, 0x11u, 0x45u, 0x4eu, 0x54u, 0x45u,
    0x52u, 0x20u, 0x4fu, 0x50u, 0x53u, 0x4cu, 0x41u, 0x41u, 0x4eu, 0x20u, 0x42u,
    0x53u, 0x20u, 0x57u, 0x49u, 0x53u, 0x20u, 0x53u, 0x54u, 0x4fu, 0x50u, 0x20u,
    0x54u, 0x45u, 0x52u, 0x55u, 0x47u, 0x20u, 0x01u, 0x00u, 0xffu, 0x32u, 0x0fu,
    0x20u, 0x03u, 0x15u, 0x0fu, 0x4bu, 0x00u, 0x10u, 0x50u, 0x20u, 0x20u, 0x20u,
    0x20u, 0x20u,
};

/** Compressed wifi scan screen; row text retained for review.
 * 1: title  P2000T  WIFI-INSTELLING
 * 2: title    WIFI-NETWERKEN ZOEKEN...
 * 3: panel  LINK ACTIEF - POLL 0000 |
 * 4: panel  NETWERKEN GEVONDEN: 0
 * 5: title    RADIO: STARTEN
 * 6: rule
 */
static const uint8_t wifi_scan_lz4[] = {
    0x1fu, 0x20u, 0x01u, 0x00u, 0x14u, 0xfdu, 0x0cu, 0x04u, 0x1du, 0x07u, 0x20u,
    0x50u, 0x32u, 0x30u, 0x30u, 0x30u, 0x54u, 0x20u, 0x20u, 0x57u, 0x49u, 0x46u,
    0x49u, 0x2du, 0x49u, 0x4eu, 0x53u, 0x54u, 0x45u, 0x4cu, 0x4cu, 0x49u, 0x4eu,
    0x47u, 0x28u, 0x00u, 0x03u, 0x22u, 0x00u, 0xf6u, 0x04u, 0x4eu, 0x45u, 0x54u,
    0x57u, 0x45u, 0x52u, 0x4bu, 0x45u, 0x4eu, 0x20u, 0x5au, 0x4fu, 0x45u, 0x4bu,
    0x45u, 0x4eu, 0x2eu, 0x2eu, 0x2eu, 0x28u, 0x00u, 0xfau, 0x0fu, 0x07u, 0x1du,
    0x04u, 0x20u, 0x4cu, 0x49u, 0x4eu, 0x4bu, 0x20u, 0x41u, 0x43u, 0x54u, 0x49u,
    0x45u, 0x46u, 0x20u, 0x2du, 0x20u, 0x50u, 0x4fu, 0x4cu, 0x4cu, 0x20u, 0x30u,
    0x30u, 0x30u, 0x30u, 0x20u, 0x7cu, 0x20u, 0x28u, 0x00u, 0x06u, 0x49u, 0x00u,
    0xbfu, 0x47u, 0x45u, 0x56u, 0x4fu, 0x4eu, 0x44u, 0x45u, 0x4eu, 0x3au, 0x20u,
    0x30u, 0xa0u, 0x00u, 0x00u, 0xffu, 0x01u, 0x20u, 0x20u, 0x52u, 0x41u, 0x44u,
    0x49u, 0x4fu, 0x3au, 0x20u, 0x53u, 0x54u, 0x41u, 0x52u, 0x54u, 0x45u, 0x4eu,
    0xc8u, 0x00u, 0x01u, 0x2fu, 0x14u, 0x73u, 0x01u, 0x00u, 0x13u, 0x1fu, 0x20u,
    0x01u, 0x00u, 0xffu, 0xffu, 0x91u, 0x50u, 0x20u, 0x20u, 0x20u, 0x20u, 0x20u,
};
